lilDyNo94/Projet-machine-de-Turing/Projet Elec - Machine de Turing/Ressources/Analyse_fonctionnelle/Bêtes_a_cornes.png

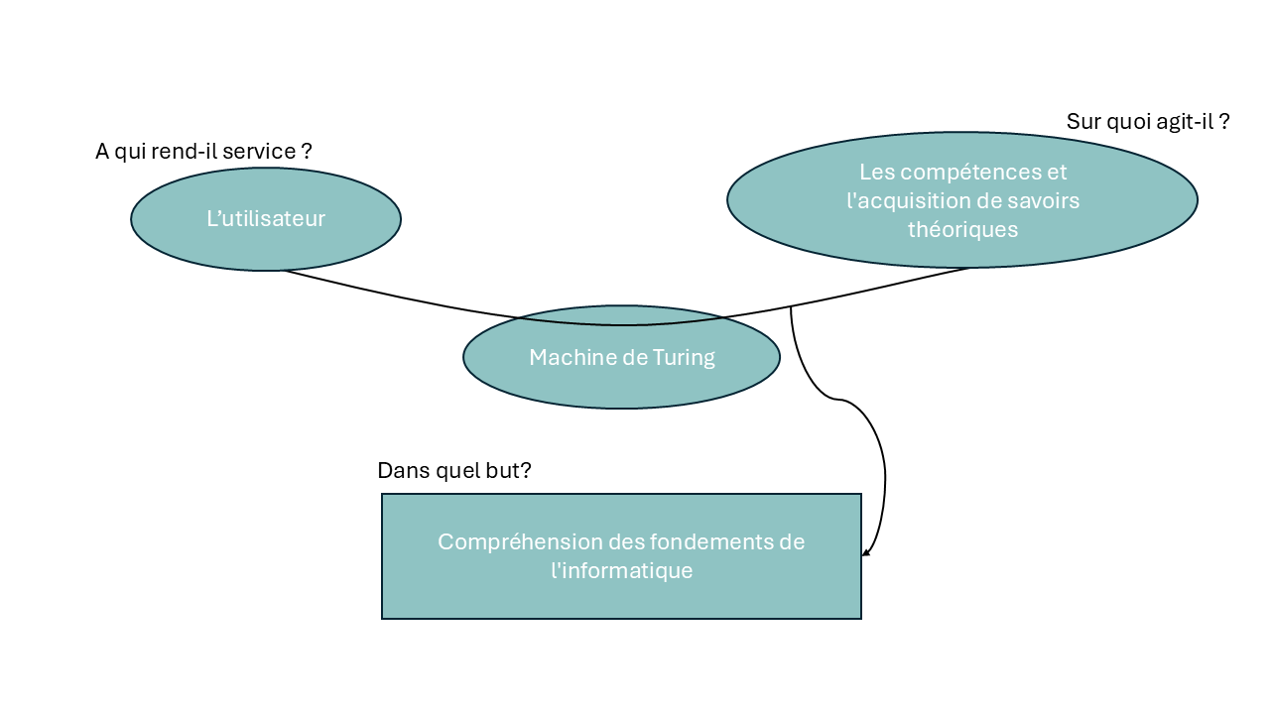
Projet Elec - Machine de Turing/Ressources/Analyse_fonctionnelle/Bêtes_a_cornes.png
