lilDyNo94/Projet-machine-de-Turing/Projet Elec - Machine de Turing/Ressources/Analyse_fonctionnelle/Matrice_Moscow.png

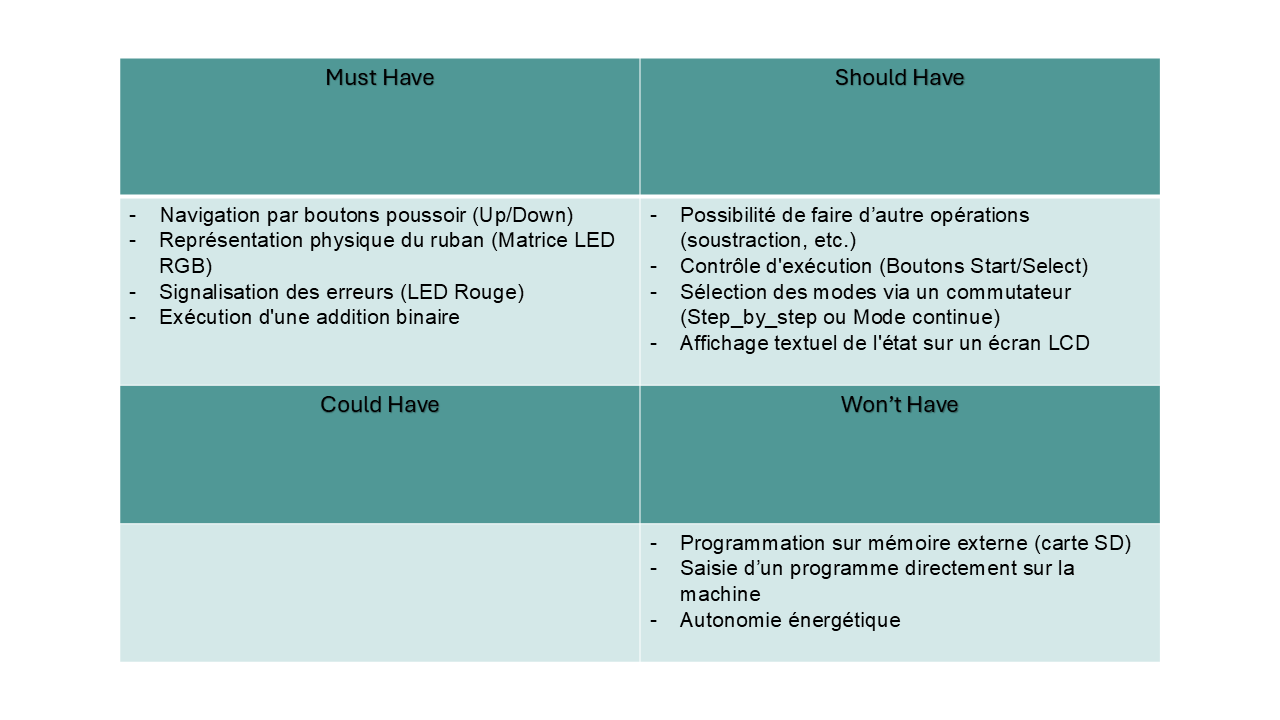
Projet Elec - Machine de Turing/Ressources/Analyse_fonctionnelle/Matrice_Moscow.png
