lilDyNo94/Projet-machine-de-Turing/Projet Elec - Machine de Turing/Ressources/Analyse_fonctionnelle/SF2D_FP2.png

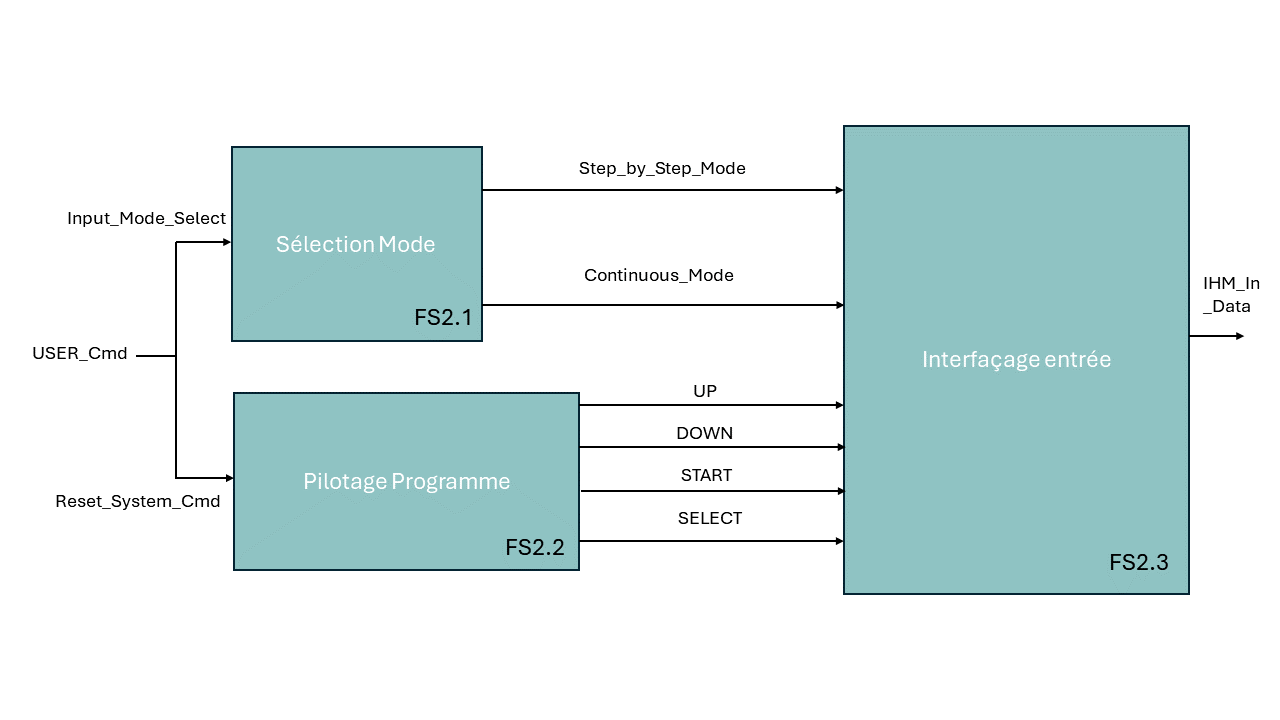
Projet Elec - Machine de Turing/Ressources/Analyse_fonctionnelle/SF2D_FP2.png
