lilDyNo94/Projet-machine-de-Turing/Projet Elec - Machine de Turing/Ressources/Analyse_fonctionnelle/SF2D_FP3.png

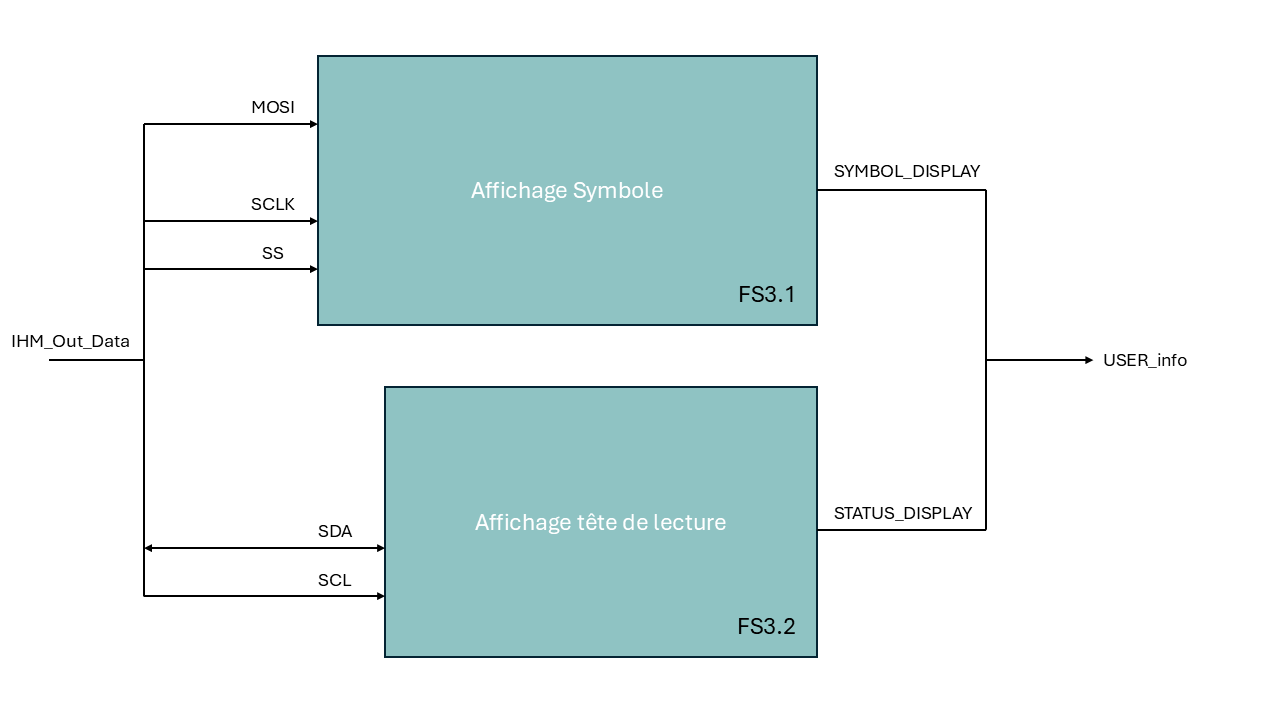
Projet Elec - Machine de Turing/Ressources/Analyse_fonctionnelle/SF2D_FP3.png
