lilDyNo94/Projet-machine-de-Turing/Projet Elec - Machine de Turing/Ressources/Analyse_fonctionnelle/SFN1.png

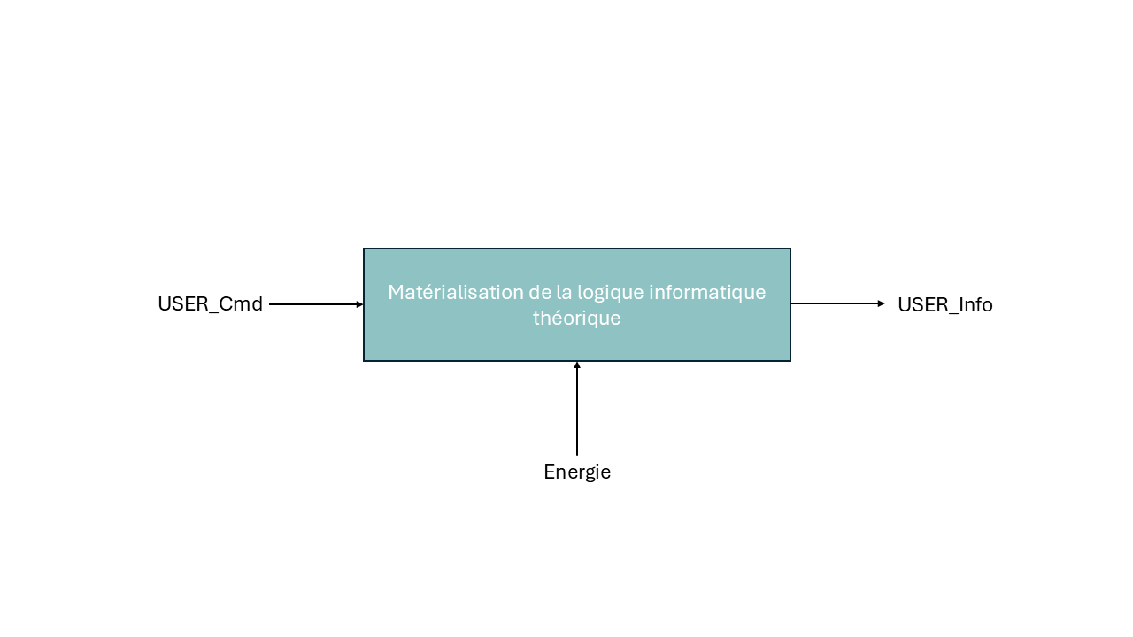
Projet Elec - Machine de Turing/Ressources/Analyse_fonctionnelle/SFN1.png
