lilDyNo94/Projet-machine-de-Turing/Projet Elec - Machine de Turing/Schéma_élec/schema_struturel.png

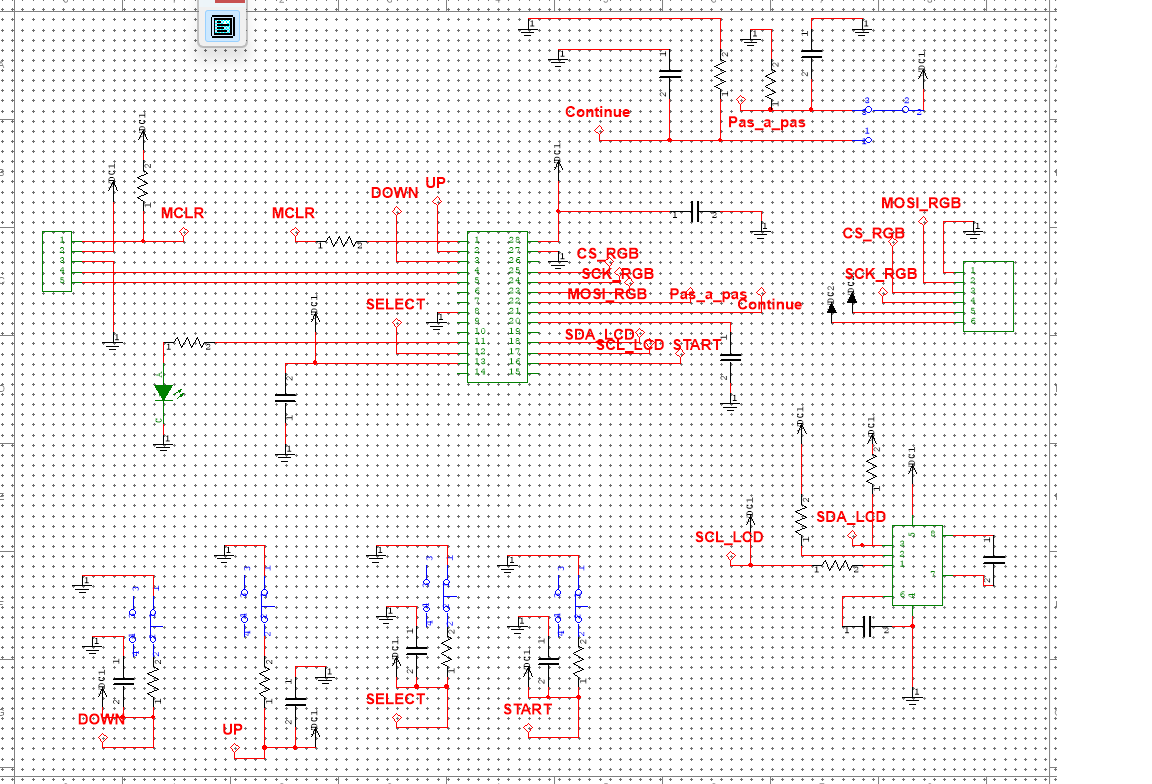
Projet Elec - Machine de Turing/Schéma_élec/schema_struturel.png
