lilDyNo94/Projet-machine-de-Turing/Projet Elec - Machine de Turing/Schéma_élec/Schéma_élec_V2.png

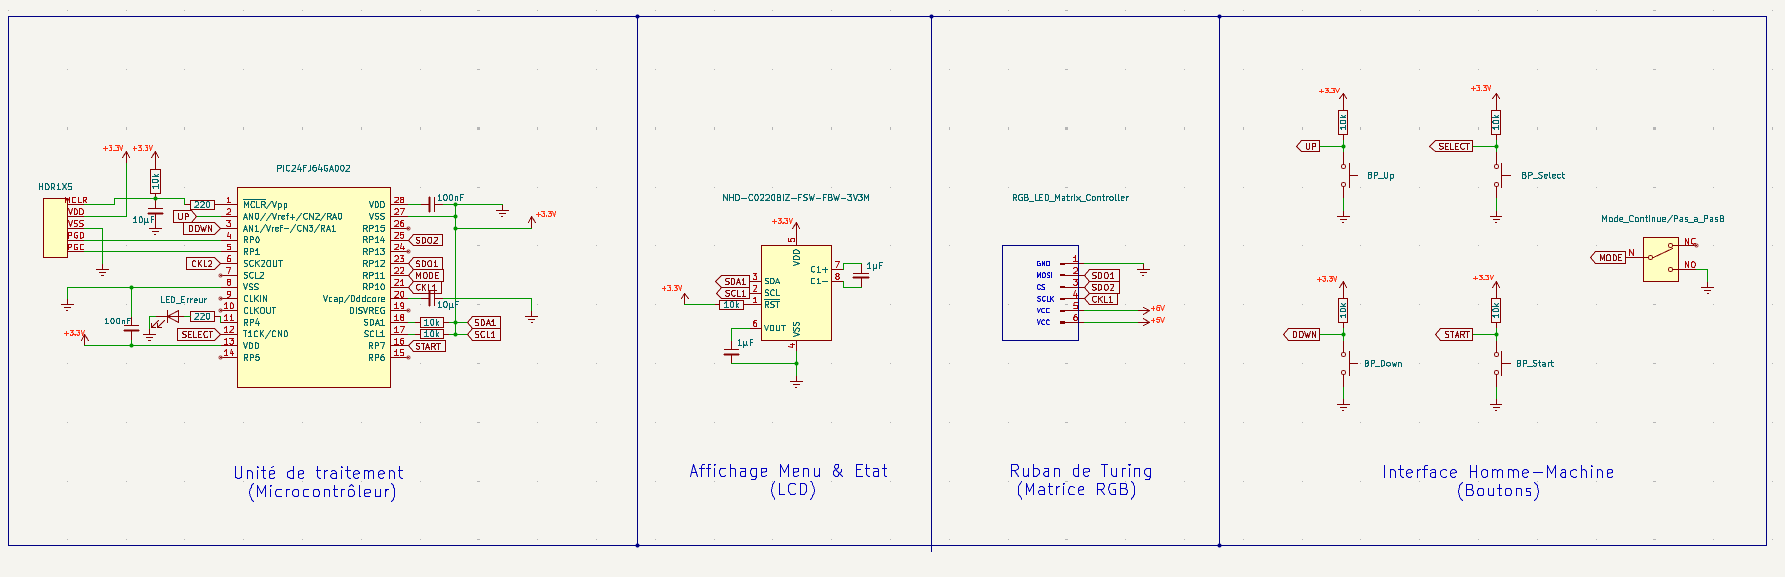
Projet Elec - Machine de Turing/Schéma_élec/Schéma_élec_V2.png
