lilDyNo94/Projet-machine-de-Turing/Projet Elec - Machine de Turing/KiCad/Machine_de_turing/Schema.kicad_sch

## KiCad design Projet Elec - Machine de Turing/KiCad/Machine_de_turing/Schema.kicad_sch (2026-06-17)

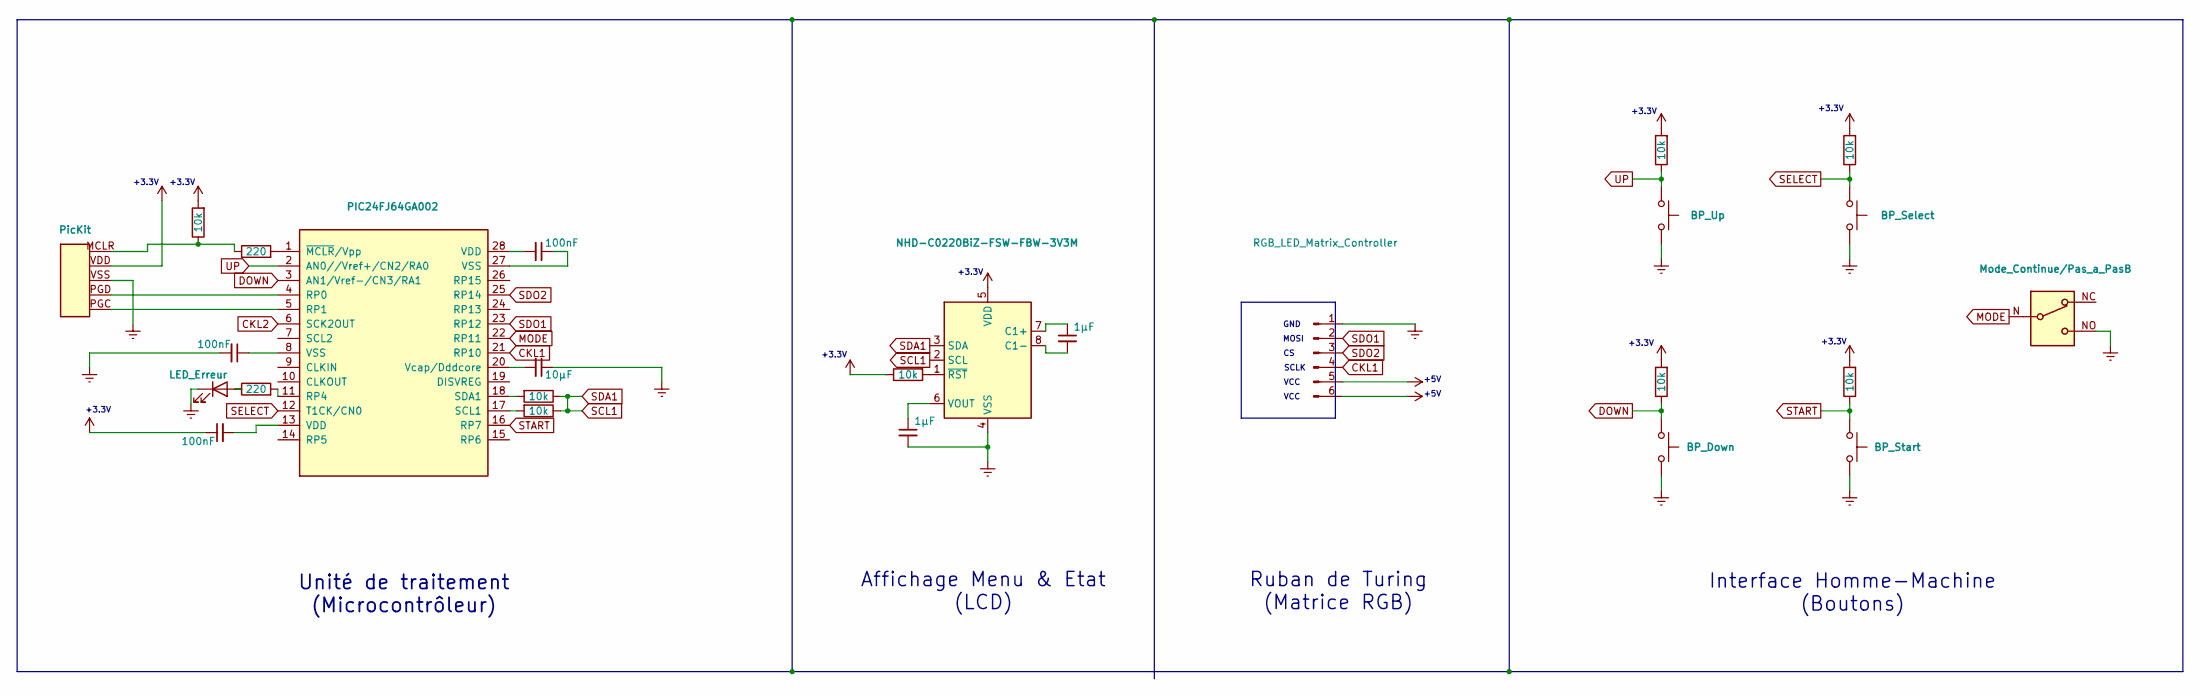
[picture p101: schematic Schema.kicad_sch]

Parts:
1µF, 10µF, 100nF: Capacitor
J1: RGB_LED_Matrix_Controller
Mode_Continue/Pas_a_Pas: Levier
PicKit: DIN41612_02x05_AB_EvenPins
R1, R2: 10k
R3: 220
U=5V: PIC24FJ64GA002

Connections:
CKL1: J1.4, U=5V.21 (RP10)
CKL2: U=5V.6 (SCK2OUT)
DOWN: U=5V.3 (AN1/Vref-/CN3/RA1)
MODE: Mode_Continue/Pas_a_Pas.N, U=5V.22 (RP11)
unnamed: 1µF.2, 10µF.1, J1.1, J1.5, J1.6
unnamed: 10µF.2, U=5V.20 (Vcap/Dddcore)
unnamed: 100nF.1, U=5V.8 (VSS), U=5V.27 (VSS)
unnamed: 100nF.2, U=5V.13 (VDD), U=5V.28 (VDD)
unnamed: PicKit.PGC, U=5V.5 (RP1)
unnamed: PicKit.PGD, U=5V.4 (RP0)
unnamed: R1.2, U=5V.17 (SCL1)
unnamed: R2.2, U=5V.18 (SDA1)
unnamed: R3.2, U=5V.11 (RP4)
SCL1: R1.1, R2.1
SDO1: J1.2, U=5V.23 (RP12)
SDO2: J1.3, U=5V.25 (RP14)
SELECT: U=5V.12 (T1CK/CN0)
START: U=5V.16 (RP7)
UP: U=5V.2 (AN0//Vref+/CN2/RA0)

Notes on the sheet:
+3.3V
Ruban de Turing (Matrice RGB)
Unité de traitement (Microcontrôleur)
Interface Homme-Machine (Boutons)
GND
+5V
Affichage Menu & Etat (LCD)
VCC
SCLK
MOSI
